odelayIO/puch-Power-Controller-Board/doc/20260208_193109808_iOS.jpg

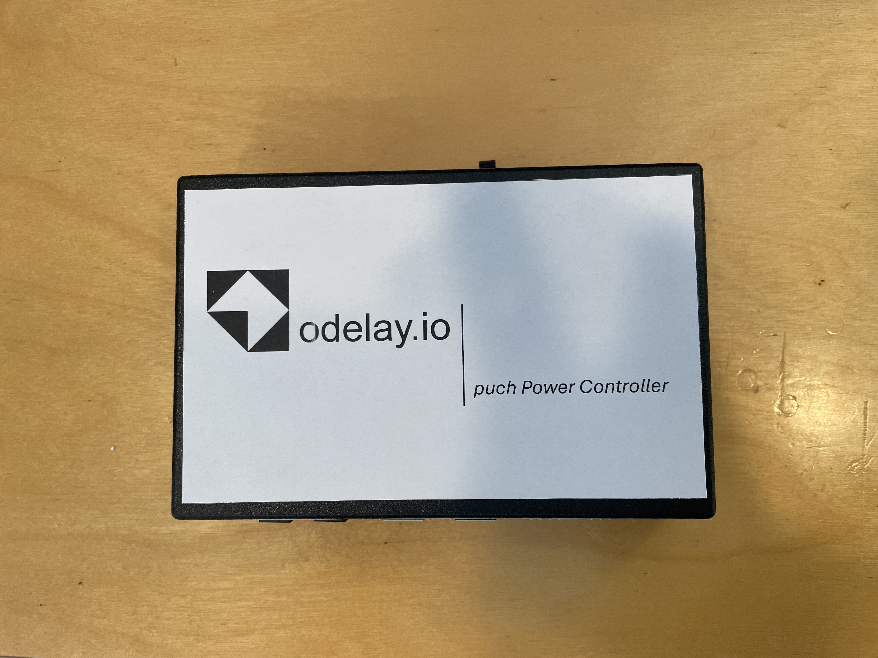
doc/20260208_193109808_iOS.jpg
